todbot/blink1mk3/schematic/blink1_trinket0.brd

## EAGLE design schematic/blink1_trinket0.brd (2020-03-10)

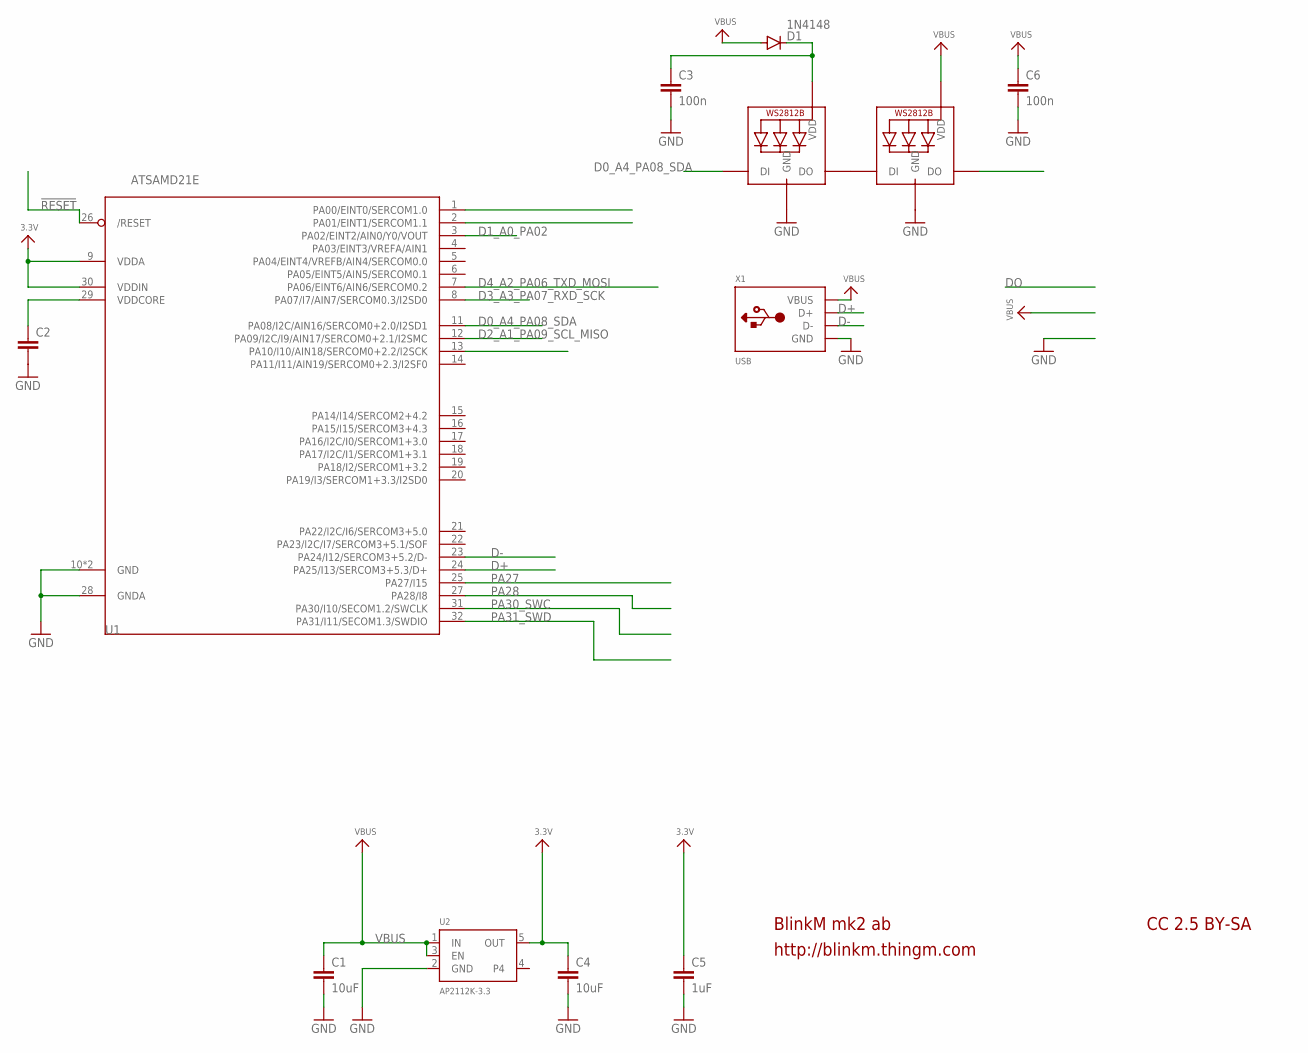
[picture p16: schematic blink1_trinket0.sch]

Parts:
C1, C4: 10uF; C0402
C2: C-EUC0402; C0402
C3, C6: 100n; C0402
C5: 1uF; C0402
D1: 1N4148; SOD523
L1, L2: WS2812B3535; LED3535
U1: ATSAMD21E; QFN32_5MM
U2: AP2112K-3.3; SOT23-5
X1: USB; MOLEX-48037-1000

Connections:
3.3V: C4.1, C5.1, U1.9 (VDDA), U1.30 (VDDIN), U2.5 (OUT)
!RESET: U1.26 (/RESET)
A3: U1.1 (PA00/EINT0/SERCOM1.0)
D0_A4_PA08_SDA: L1.1 (DI), U1.11 (PA08/I2C/AIN16/SERCOM0+2.0/I2SD1)
D1_A0_PA02: U1.3 (PA02/EINT2/AIN0/Y0/VOUT)
D2_A1_PA09_SCL_MISO: U1.12 (PA09/I2C/I9/AIN17/SERCOM0+2.1/I2SMC)
D3_A3_PA07_RXD_SCK: U1.8 (PA07/I7/AIN7/SERCOM0.3/I2SD0)
D4_A2_PA06_TXD_MOSI: U1.7 (PA06/EINT6/AIN6/SERCOM0.2)
D+: U1.24 (PA25/I13/SERCOM3+5.3/D+), X1.3 (D+)
D-: U1.23 (PA24/I12/SERCOM3+5.2/D-), X1.2 (D-)
DO: L2.3 (DO)
GND: C1.2, C2.2, C3.2, C4.2, C5.2, C6.2, L1.4 (GND), L2.4 (GND), U1.10 (GND), U1.28 (GNDA), U1.33 (GND), U2.2 (GND), X1.4 (GND)
unnamed: C3.1, D1.C, L1.2 (VDD)
unnamed: L1.3 (DO), L2.1 (DI)
PA27: U1.25 (PA27/I15)
PA28: U1.27 (PA28/I8)
PA30_SWC: U1.31 (PA30/I10/SECOM1.2/SWCLK)
PA31_SWD: U1.32 (PA31/I11/SECOM1.3/SWDIO)
VBUS: C1.1, C6.1, D1.A, L2.2 (VDD), U2.1 (IN), U2.3 (EN), X1.1 (VBUS)
VDDCORE: C2.1, U1.29 (VDDCORE)

Notes on the sheet:
BlinkM mk2 ab
http://blinkm.thingm.com
CC 2.5 BY-SA

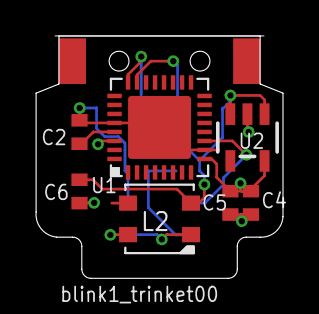
[picture p17: board blink1_trinket0.brd from above]

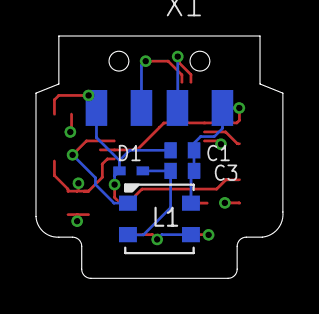
[picture p18: board blink1_trinket0.brd from below]

Board: 4 copper layers, 13.7 x 13.5 mm, 12 parts (5 on the bottom side), 9 nets.
