todbot/blink1mk3/schematic/blink1micro-programming-jig.brd

## EAGLE design schematic/blink1micro-programming-jig.brd (2018-11-15)

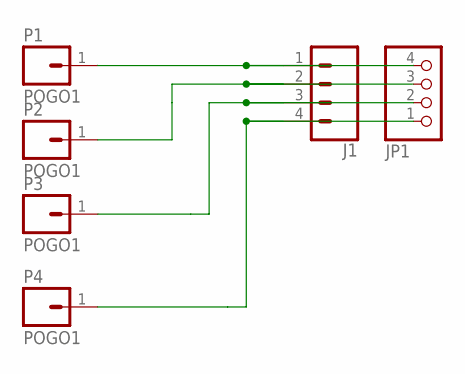
[picture p21: schematic blink1micro-programming-jig.sch]

Parts:
J1: CONN_04; 1X04
JP1: PINHD-1X4/90; 1X04/90
P1, P2, P3, P4: POGO1; MILLMAX-0928-POGO-THRU

Connections:
unnamed: J1.1, JP1.4, P1.1
unnamed: J1.2, JP1.3, P2.1
unnamed: J1.3, JP1.2, P3.1
unnamed: J1.4, JP1.1, P4.1

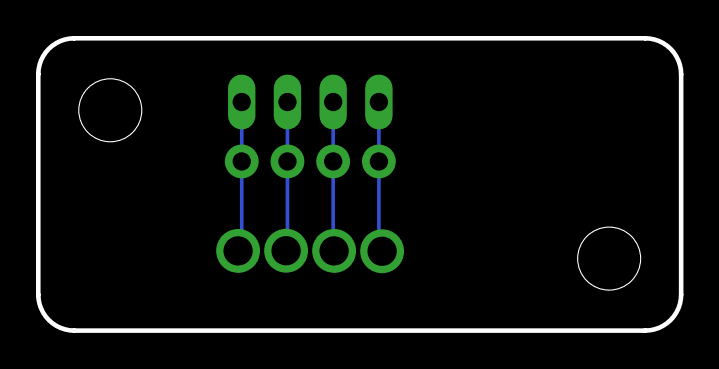
[picture p22: board blink1micro-programming-jig.brd from above]

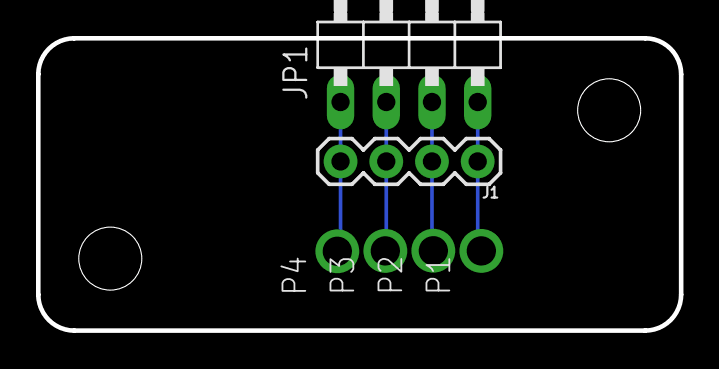
[picture p23: board blink1micro-programming-jig.brd from below]

Board: 2 copper layers, 35.7 x 16.2 mm, 6 parts (6 on the bottom side), 4 nets.
