todbot/blink1mk3/schematic/card/blink1mk3_card1.brd

## EAGLE design schematic/card/blink1mk3_card1.brd (2018-05-24)

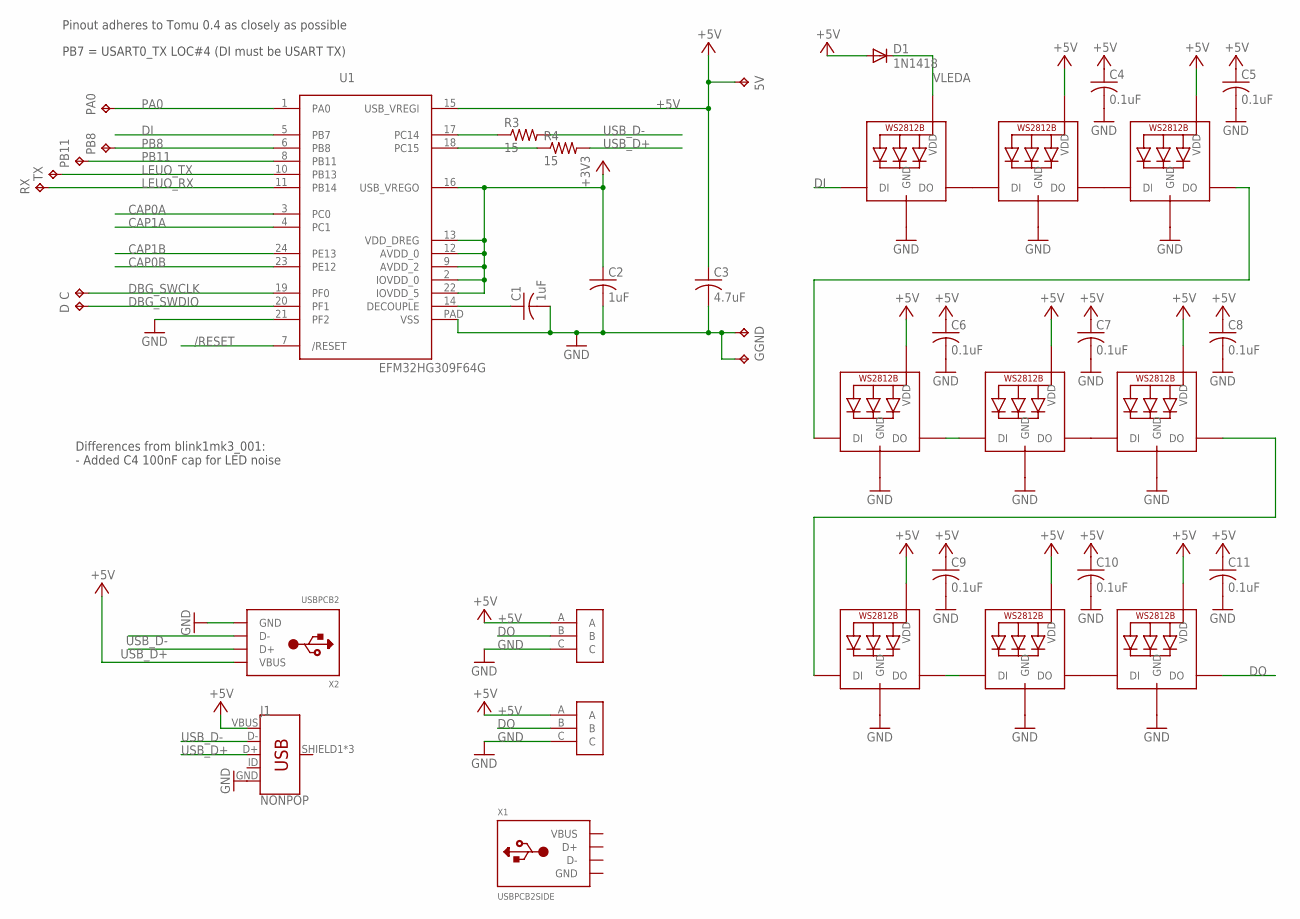
[picture p24: schematic blink1mk3_card1.sch]

Parts:
5V: TPTP15R; TP15R
C: TPTP15R; TP15R
C1, C2: 1uF; C0603
C3: 4.7uF; C0603
C4, C5, C6, C7, C8, C9, C10, C11: 0.1uF; C0603
D: TPTP15R; TP15R
D1: 1N1418; SOD523
G: TPTP14SQ; TP14SQ
GND: TPTP14SQ; TP14SQ
J1: NONPOP; USB-B-MICRO-SMD
LED1, LED2, LED3, LED4, LED5, LED6, LED7, LED8, LED9: SK6812MINI; LED3535
PA0: TPTP15R; TP15R
PB8, PB11: TPTP15R; TP15R
R3, R4: 15; R0603
RX: TPTP15R; TP15R
TX: TPTP15R; TP15R
U1: EFM32HG309F64G; QFN24PAD
U$1, U$2: LED_STRIP_3P; LEDSTRIP-3P
X1: USBPCB2SIDE; USB-A-PCB-TWOSIDED
X2: USBPCB2; USB-A-PCB-2

Connections:
+3V3: C2.1, U1.2 (IOVDD_0), U1.9 (AVDD_2), U1.12 (AVDD_0), U1.13 (VDD_DREG), U1.16 (USB_VREGO), U1.22 (IOVDD_5)
+5V: 5V.TP, C3.1, C4.1, C5.1, C6.1, C7.1, C8.1, C9.1, C10.1, C11.1, D1.A, J1.VBUS, LED2.2 (VDD), LED3.2 (VDD), LED4.2 (VDD), LED5.2 (VDD), LED6.2 (VDD), LED7.2 (VDD), LED8.2 (VDD), LED9.2 (VDD), U1.15 (USB_VREGI), U$1.A, U$2.A, X2.5V (VBUS)
/RESET: U1.7 (/RESET)
CAP0A: U1.3 (PC0)
CAP0B: U1.23 (PE12)
CAP1A: U1.4 (PC1)
CAP1B: U1.24 (PE13)
DBG_SWCLK: C.TP, U1.19 (PF0)
DBG_SWDIO: D.TP, U1.20 (PF1)
DECOUPLE: C1.1, U1.14 (DECOUPLE)
DI: LED1.1 (DI), U1.5 (PB7)
DO: LED9.3 (DO), U$1.B, U$2.B
GND: C1.2, C2.2, C3.2, C4.2, C5.2, C6.2, C7.2, C8.2, C9.2, C10.2, C11.2, G.TP, GND.TP, J1.GND, LED1.4 (GND), LED2.4 (GND), LED3.4 (GND), LED4.4 (GND), LED5.4 (GND), LED6.4 (GND), LED7.4 (GND), LED8.4 (GND), LED9.4 (GND), U1.21 (PF2), U1.PAD (VSS), U$1.C, U$2.C, X1.GND@1 (GND), X1.GND@2 (GND), X1.GND@3 (GND), X2.GND
LEUO_RX: RX.TP, U1.11 (PB14)
LEUO_TX: TX.TP, U1.10 (PB13)
unnamed: LED1.3 (DO), LED2.1 (DI)
unnamed: LED7.3 (DO), LED8.1 (DI)
unnamed: LED4.3 (DO), LED5.1 (DI)
unnamed: LED5.3 (DO), LED6.1 (DI)
unnamed: LED2.3 (DO), LED3.1 (DI)
unnamed: LED3.3 (DO), LED4.1 (DI)
unnamed: LED8.3 (DO), LED9.1 (DI)
unnamed: LED6.3 (DO), LED7.1 (DI)
PA0: PA0.TP, U1.1 (PA0)
PB8: PB8.TP, U1.6 (PB8)
PB11: PB11.TP, U1.8 (PB11)
RUSB_D+: R4.1, U1.18 (PC15)
RUSB_D-: R3.1, U1.17 (PC14)
USB_D+: J1.D+, R4.2, X2.USB_P (D+)
USB_D-: J1.D-, R3.2, X2.USB_M (D-)
VBUS: X1.5V@1 (VBUS), X1.5V@2 (VBUS), X1.5V@3 (VBUS)
VLEDA: D1.C, LED1.2 (VDD)

Notes on the sheet:
PB7 = USART0_TX LOC#4 (DI must be USART TX)
Pinout adheres to Tomu 0.4 as closely as possible
Differences from blink1mk3_001: - Added C4 100nF cap for LED noise
