todbot/blink1mk3/schematic/card/blink1mk3_card1.brd

## EAGLE design schematic/card/blink1mk3_card1.brd (continued)

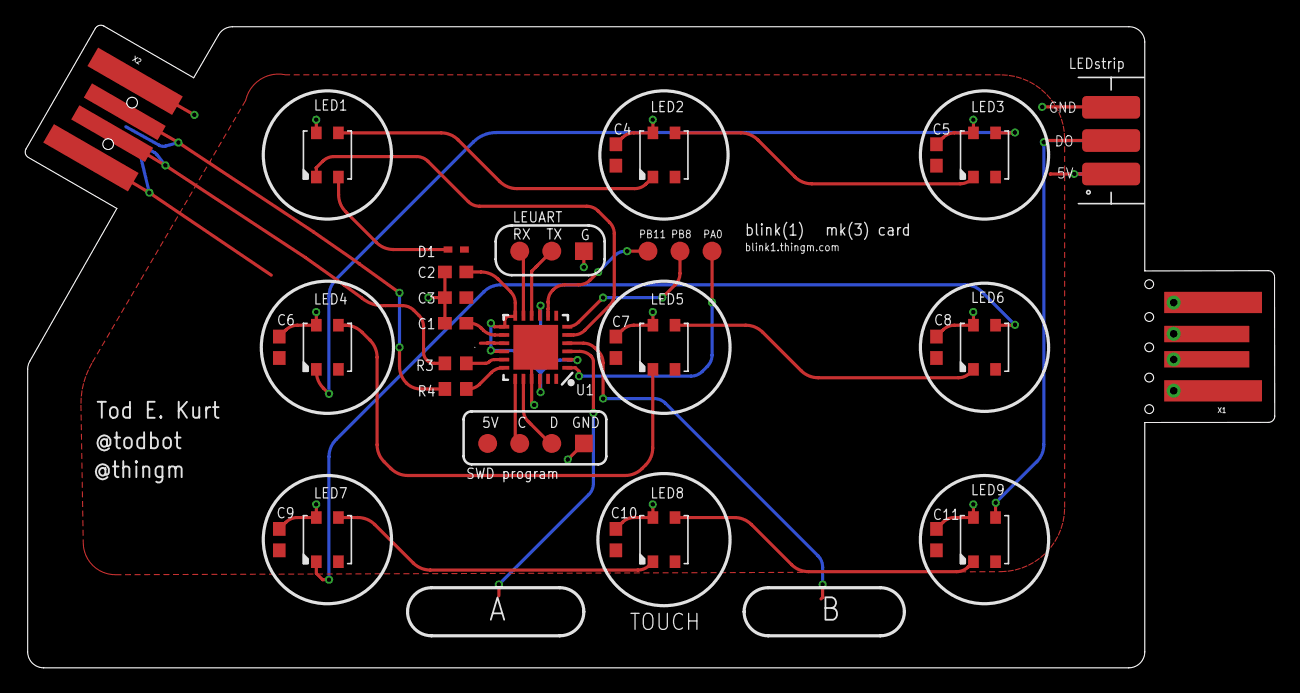
[picture p25: board blink1mk3_card1.brd from above]

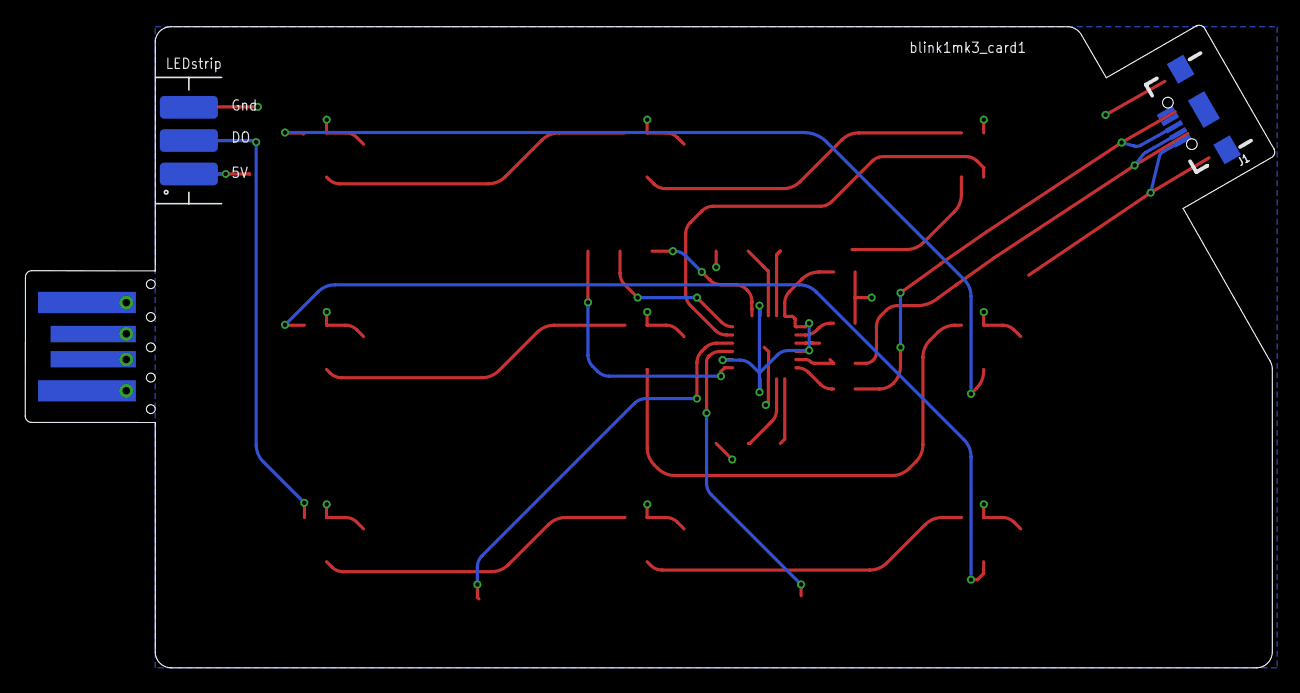
[picture p26: board blink1mk3_card1.brd from below]

Board: 2 copper layers, 99.0 x 50.9 mm, 39 parts (2 on the bottom side), 27 nets.
