todbot/blink1mk3/schematic/blink1mk3_001.brd

## EAGLE design schematic/blink1mk3_001.brd (2018-03-21)

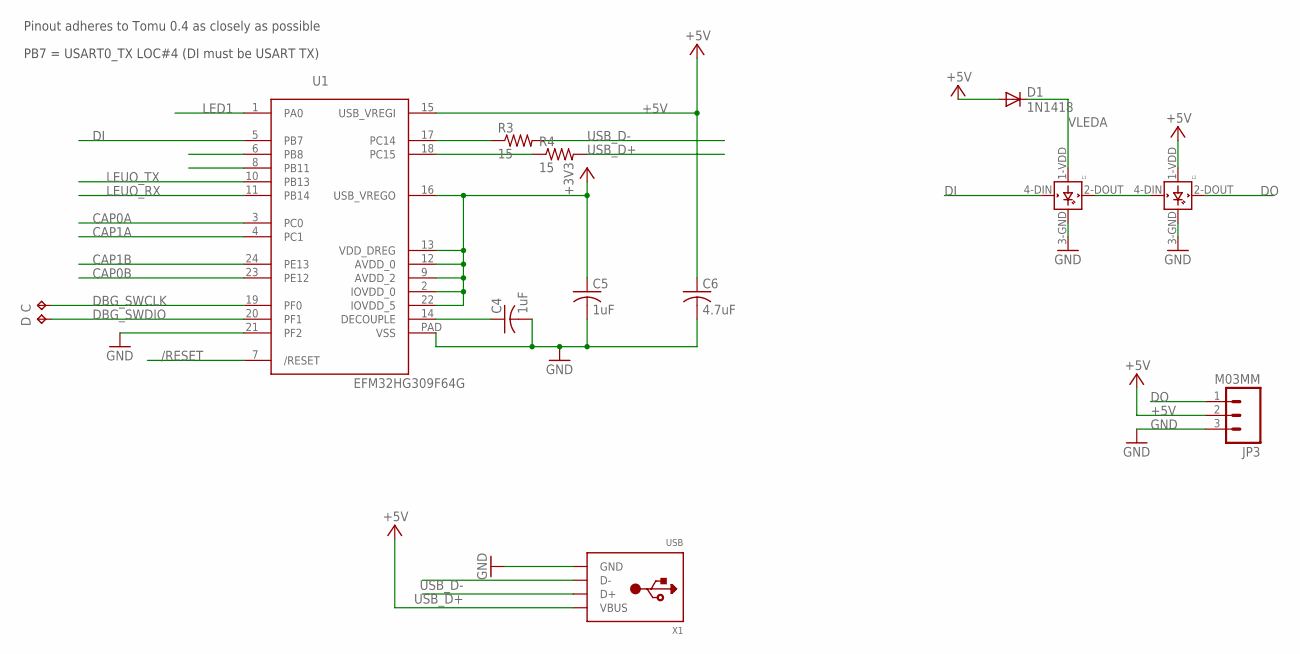
[picture p27: schematic blink1mk3_001.sch]

Parts:
C: TPTP10R; TP10R
C4, C5: 1uF; C0402
C6: 4.7uF; C0402
D: TPTP10R; TP10R
D1: 1N1418; SOD523
JP3: M03MM; 1X03-1.5MM
L1, L2: WS2812B
R3, R4: 15; R0402
U1: EFM32HG309F64G; QFN24PAD
X1: USB; MOLEX-48037-1000

Connections:
+3V3: C5.1, U1.2 (IOVDD_0), U1.9 (AVDD_2), U1.12 (AVDD_0), U1.13 (VDD_DREG), U1.16 (USB_VREGO), U1.22 (IOVDD_5)
+5V: C6.1, D1.A, JP3.2, L2.1-VDD (VDD), U1.15 (USB_VREGI), X1.1 (VBUS)
/RESET: U1.7 (/RESET)
CAP0A: U1.3 (PC0)
CAP0B: U1.23 (PE12)
CAP1A: U1.4 (PC1)
CAP1B: U1.24 (PE13)
DBG_SWCLK: C.TP, U1.19 (PF0)
DBG_SWDIO: D.TP, U1.20 (PF1)
DECOUPLE: C4.1, U1.14 (DECOUPLE)
DI: L1.4-DIN (DIN), U1.5 (PB7)
DO: JP3.1, L2.2-DOUT (DOUT)
GND: C4.2, C5.2, C6.2, JP3.3, L1.3-GND (GND), L2.3-GND (GND), U1.21 (PF2), U1.PAD (VSS), X1.4 (GND)
LED1: U1.1 (PA0)
LEUO_RX: U1.11 (PB14)
LEUO_TX: U1.10 (PB13)
unnamed: L1.2-DOUT (DOUT), L2.4-DIN (DIN)
RUSB_D+: R4.1, U1.18 (PC15)
RUSB_D-: R3.1, U1.17 (PC14)
USB_D+: R4.2, X1.3 (D+)
USB_D-: R3.2, X1.2 (D-)
VLEDA: D1.C, L1.1-VDD (VDD)

Notes on the sheet:
PB7 = USART0_TX LOC#4 (DI must be USART TX)
Pinout adheres to Tomu 0.4 as closely as possible

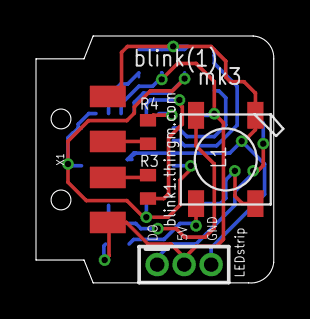
[picture p28: board blink1mk3_001.brd from above]

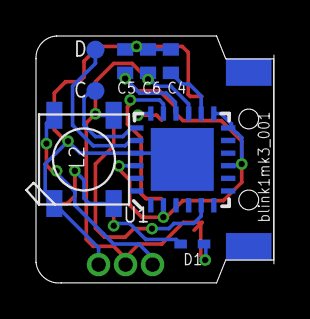
[picture p29: board blink1mk3_001.brd from below]

Board: 2 copper layers, 13.2 x 13.7 mm, 13 parts (8 on the bottom side), 14 nets.
